aditya23043/Tekken_Controller/prototype_one/imgs/WhatsApp Image 2025-02-12 at 14.55.22.jpeg

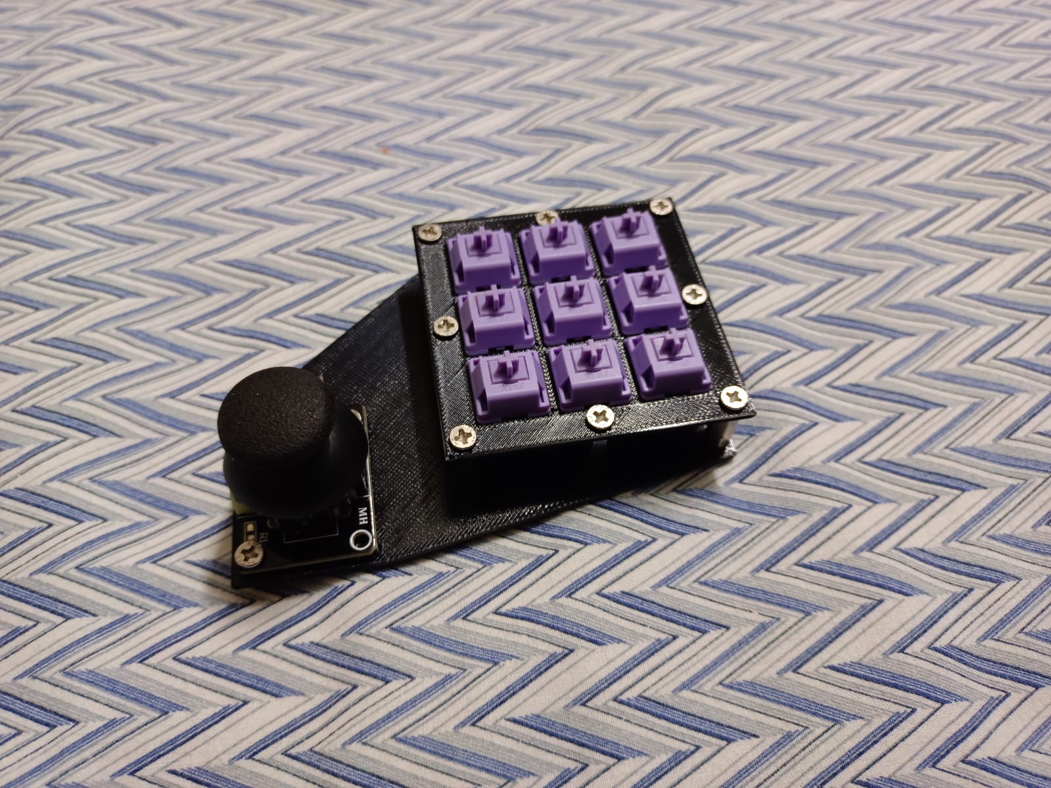
prototype_one/imgs/WhatsApp Image 2025-02-12 at 14.55.22.jpeg
