aditya23043/Tekken_Controller/prototype_three/imgs/2025-02-18_18-05.png

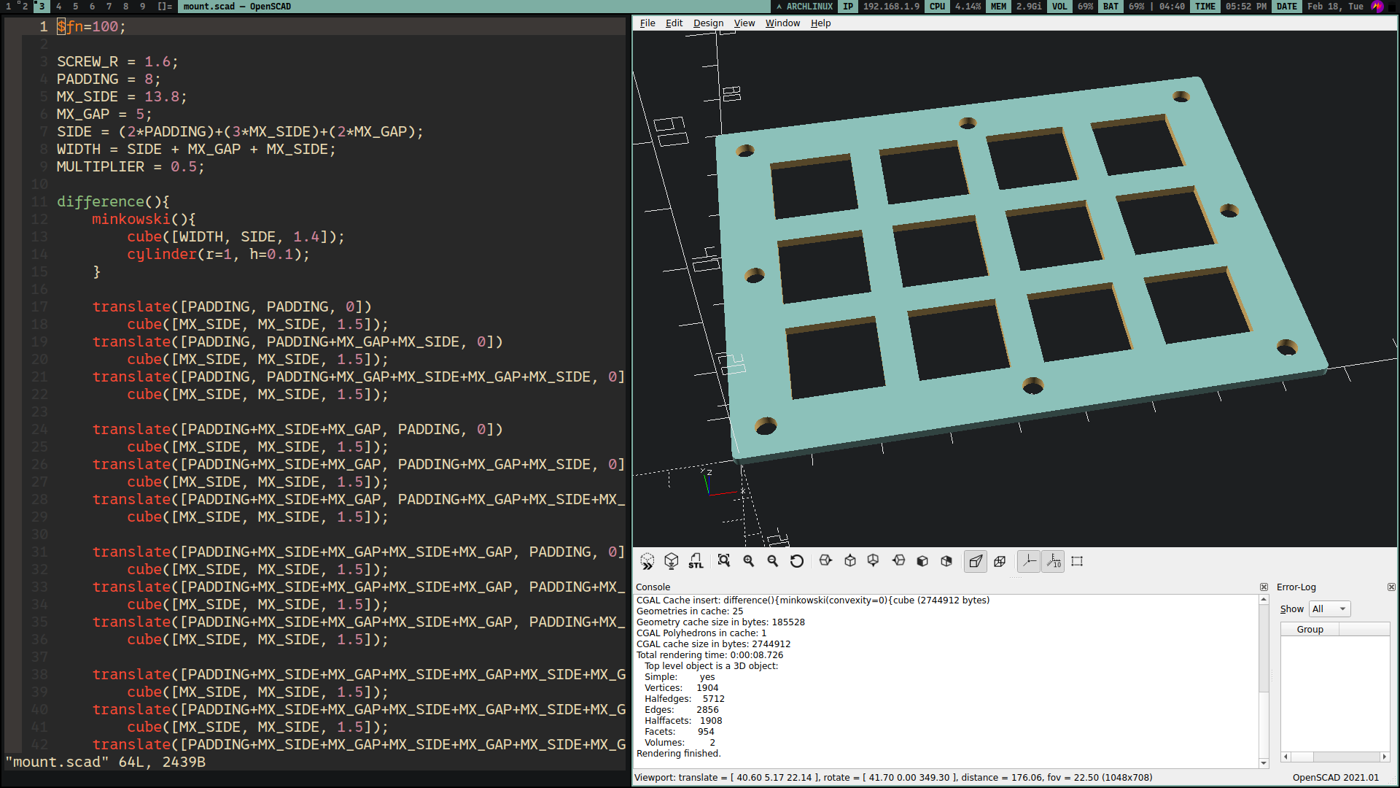
prototype_three/imgs/2025-02-18_18-05.png
